matthias-bs/Flora1/09_software/irrigation.py

"""Manual and automatic irrigation control"""
###############################################################################
# irrigation.py
#
# This module provides the Irrigation class
#
# - manual irrigation (triggered by the flag pump.busy)
# - auto irrigation, depending on
#   - current time of day (disabled during night time)
#   - various sensor values
#   - rest time after previous irrigation
#
# created: 01/2021
#
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
# History:
#
# 20210118 Extracted from flora.py
# 20210608 Added support of 2nd pump
# 20210616 Fixed auto_irrigation()
# 20230204 Coding style improvements (with pylint)
#
# To Do:
# -
#
###############################################################################

import time
from datetime import datetime
from settings import VERBOSITY, PUMP_BUSY_MAN, PUMP_BUSY_AUTO
from print_line import print_line


###############################################################################
# Irrigation class - Manual and automatic irrigation control
###############################################################################
class Irrigation:
    """Manual and automatic irrigation control"""
    #def __init__(self):
    #    """
    #    The constructor for Irrigation class.
    #    """
    #    pass

    ###################################################################################################
    # Handle manual irrigation
    ###################################################################################################
    def man_irrigation(self, settings, mqtt_client, pumps):
        """
        Manually run irrigation

        Parameters:
            settings (Settings):    instance of Settings class
            mqtt_client (Client):   MQTT client
            pump (Pump):            instance of Pump class
        """
        # Check if flag has been set (asynchronously) in 'mqtt_man_irrigation_request'
        # message callback function
        for i in range(2):
            if pumps[i].busy == PUMP_BUSY_MAN:
                print_line('Running pump #{} for {:d} seconds -->'.format(i+1, settings.irr_duration_man),
                           console=True, sd_notify=True)
                pumps[i].power_on(settings.irr_duration_man)
                pumps[i].busy = 0
                mqtt_client.publish(settings.base_topic_flora + '/man_irr_stat', str(0), qos = 1)
                print_line('<-- Running pump #{} finished, Status: {}'.format(i+1, pumps[i].status_str),
                            console=True, sd_notify=True)


    ###################################################################################################
    # Handle automatic irrigation
    ###################################################################################################
    def auto_irrigation(self, settings, sensors, pumps):
        """
        Automatically run irrigation -
        depending on sensor values, time of day and time since last irrigation

        Irrigation is run if
        - current time is not within night time range
        - all sensor data is up-to-date
        - light is below the limit <light_irr> to avoid sunburns
        - at least one moisture level is below minimum,
          but none is above maximum

        The irrigation is done immediately if the rest time <irr_rest>
        since the last (automatic) irrigation has expired, otherwise it is
        scheduled until later.

        Parameters:
            settings (Settings):    instance of Settings class
            sensors (Sensor{}):     dictionary of Sensor class
            pump (Pump):            instance of Pump class

        Returns:
            bool:   true  if irrigation is scheduled
                    false otherwise
        """
        # Skip automatic irrigation during night time
        now = datetime.now()
        nighttime_start = now.replace(hour=settings.night_begin_hr, minute=settings.night_begin_min, second=0, microsecond=0)
        nighttime_end = now.replace(hour=settings.night_end_hr, minute=settings.night_end_min, second=0, microsecond=0)

        if (now >= nighttime_start) or (now < nighttime_end):
            if VERBOSITY > 1:
                print_line("auto_irrigation: sleep time! Zzzz...")
            return [False, False]

        # Evaluate per pump
        activate = [False, False]
        for p in range(2):
            for sensor in sensors:
                if sensors[sensor].pump != p+1:
                    continue
                if not sensors[sensor].valid:
                    # At least one sensor with timeout -> bail out
                    break
                if sensors[sensor].light_il:
                    # At least one light value over irrigation limit -> bail out
                    break
                if sensors[sensor].moist_oh:
                    # At least one moisture value over range -> bail out
                    break
                if sensors[sensor].moist_ul:
                    # At least one moisture value under range -> ready!
                    activate[p] = True
                    break
                # Else: All moisture values (regarding this pump) within desired range -> nothing to do!

        schedule = [False, False]
        for p in range(2):
            if activate[p]:
                if (time.time() - pumps[p].timestamp) < settings.irr_rest:
                    # All sensor values are within range, but time since last irrigation (irr_rest)
                    # has not expired yet -> bailing out
                    if VERBOSITY > 1:
                        print_line("Auto irrigation: pump #{} scheduled.".format(p))
                    schedule[p] = True
                elif pumps[p].busy == 0:
                    # Pump has not been started manually - ready!
                    duration = settings.irr_duration_auto1 if (p == 0) else settings.irr_duration_auto2
                    print_line("Auto irrigation: running pump #{} for {:d} seconds"
                               .format(p+1, duration), console=True, sd_notify=True)
                    pumps[p].busy = PUMP_BUSY_AUTO
                    pumps[p].power_on(duration)
                    pumps[p].busy = 0
                    pumps[p].timestamp = time.time()

        return schedule
