matthias-bs/Flora1/09_software/gpio.py

"""Provide a stub as (non-functional!) replacement for RPi.GPIO"""
###############################################################################
# gpio.py
#
# This module provides a stub as (non-functional!) replacement for RPi.GPIO
# on other systems than Raspberry Pi.
#
# - tries to import RPi.GPIO as GPIO
# - if this fails, provides instance GPIO of class Gpio
#
# created: 01/2021
#
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
# History:
#
# 20210117 Extracted from flora.py
# 20230204 Coding style improvements (with pylint)
#
# To Do:
# -
#
###############################################################################

try:
    import RPi.GPIO as GPIO # pylint: disable=unused-import
    USE_GPIO_STUB = False
except (ImportError, RuntimeError):
    USE_GPIO_STUB = True
    print("Using GPIO stub")
else:
    print("Using RPi.GPIO")

#########################################################################################
# Gpio class - A stub as replacement for RPi.GPIO on other systems than Raspberry Pi
#########################################################################################
if USE_GPIO_STUB:
    class Gpio:
        def __init__(self):
            self.BCM = 0
            self.IN = 0
            self.OUT = 1
            self.LOW = 0
            self.HIGH = 1

        def setmode(self, _mode):
            pass

        def setup(self, _pin, _direction):
            pass

        def input(self, _pin):
            return False

        def output(self, _pin, _val):
            pass

# Use stub for RPi.GPIO on other systems than Raspberry Pi
if USE_GPIO_STUB:
    GPIO = Gpio()
